Amarok24/A1k-SimpleClock/Bilder/21-01-15_20-07-40_5350.jpg

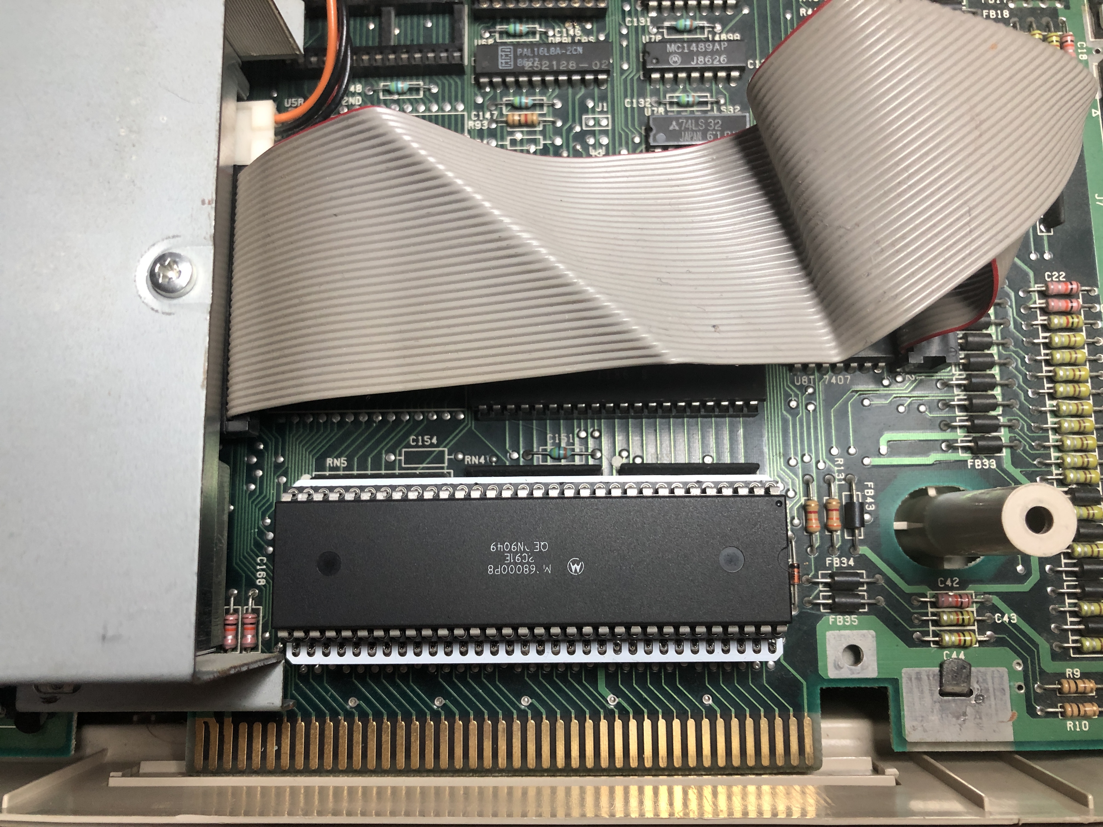
Bilder/21-01-15_20-07-40_5350.jpg
