Amarok24/A1k-SimpleClock/Bilder/21-01-15_21-09-06_5355.jpg

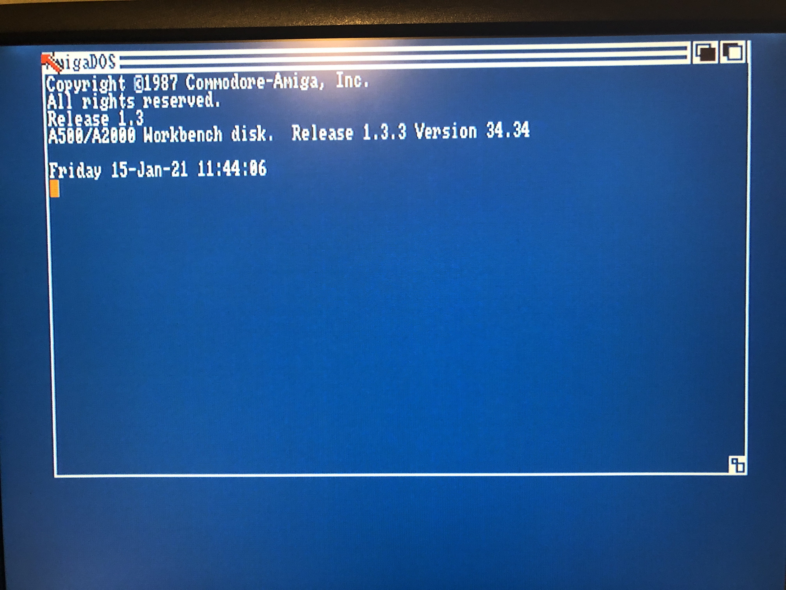
Bilder/21-01-15_21-09-06_5355.jpg
