Amarok24/A1k-SimpleClock/Bilder/21-02-26_20-54-29_5547.jpg

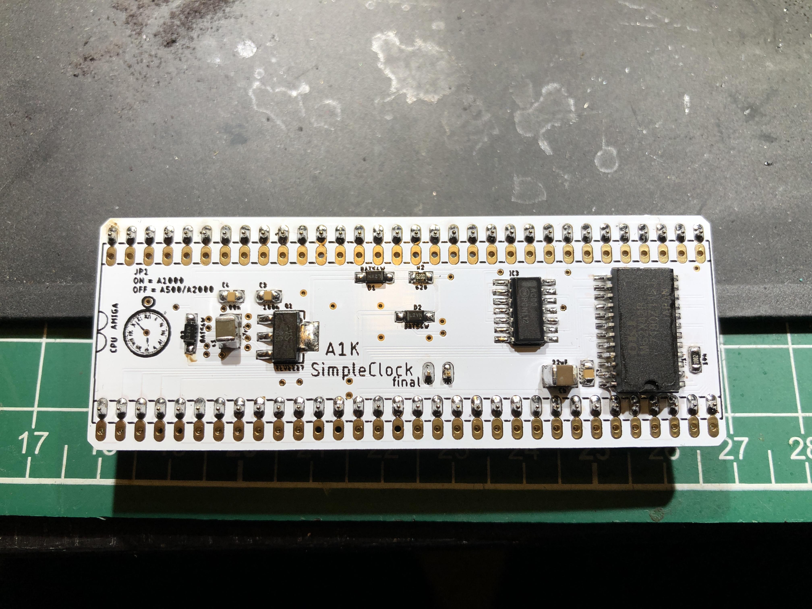
Bilder/21-02-26_20-54-29_5547.jpg
