Amarok24/A1k-SimpleClock/Bilder/21-02-26_20-54-59_5549.jpg

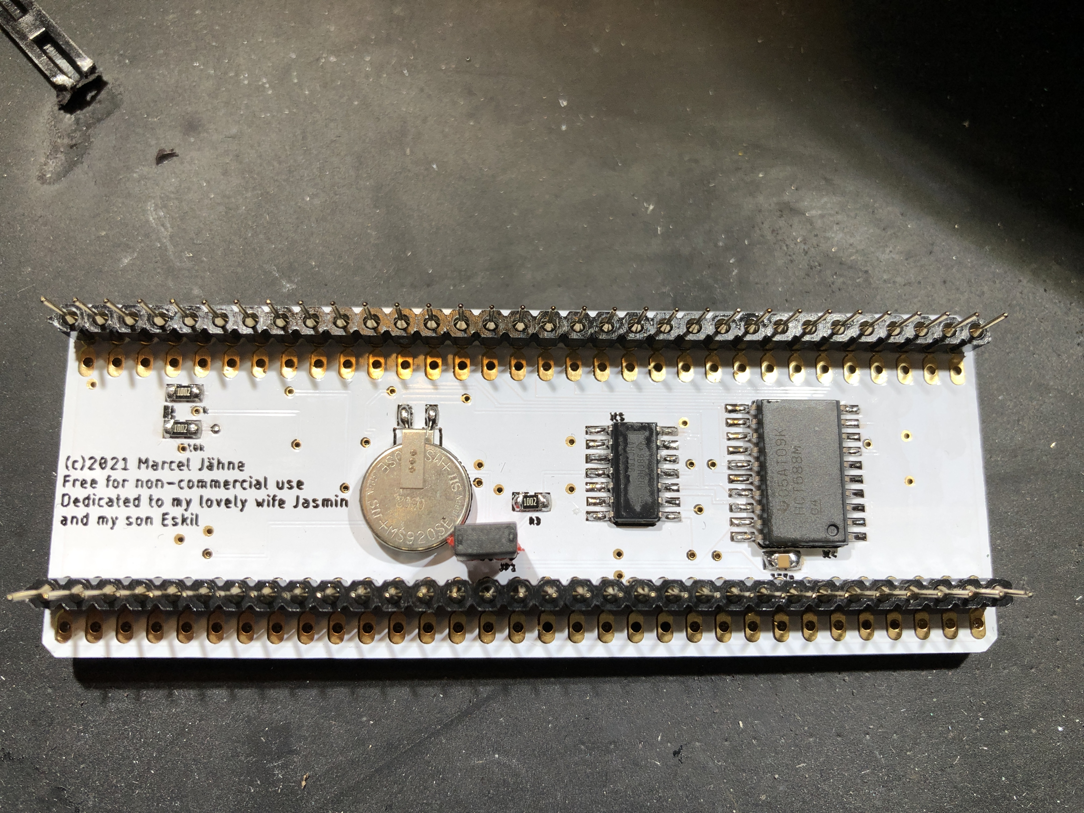
Bilder/21-02-26_20-54-59_5549.jpg
