Amarok24/A1k-SimpleClock/Bilder/21-02-26_21-03-44_5551.jpg

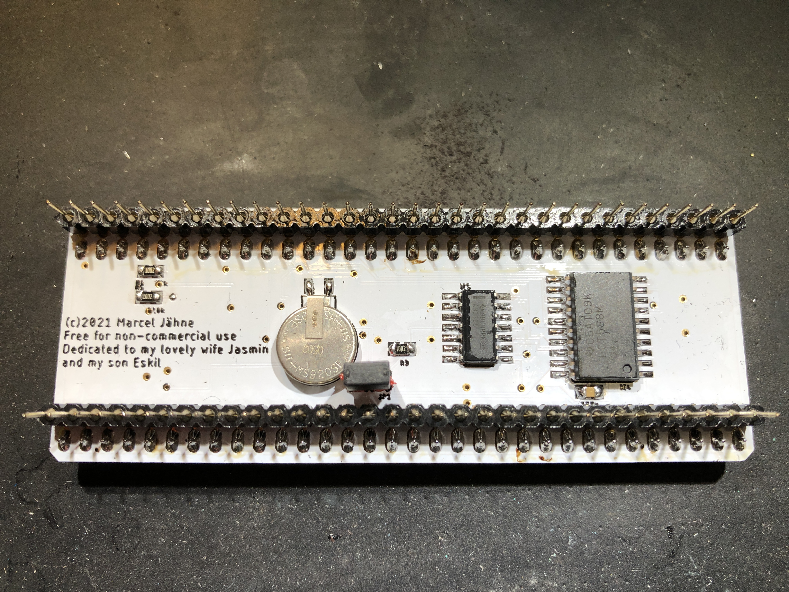
Bilder/21-02-26_21-03-44_5551.jpg
